janelia-idf/arduino_valve_controller/pcb/arduino_valve_controller.sch

## KiCad design pcb/arduino_valve_controller.sch (2019-02-07)

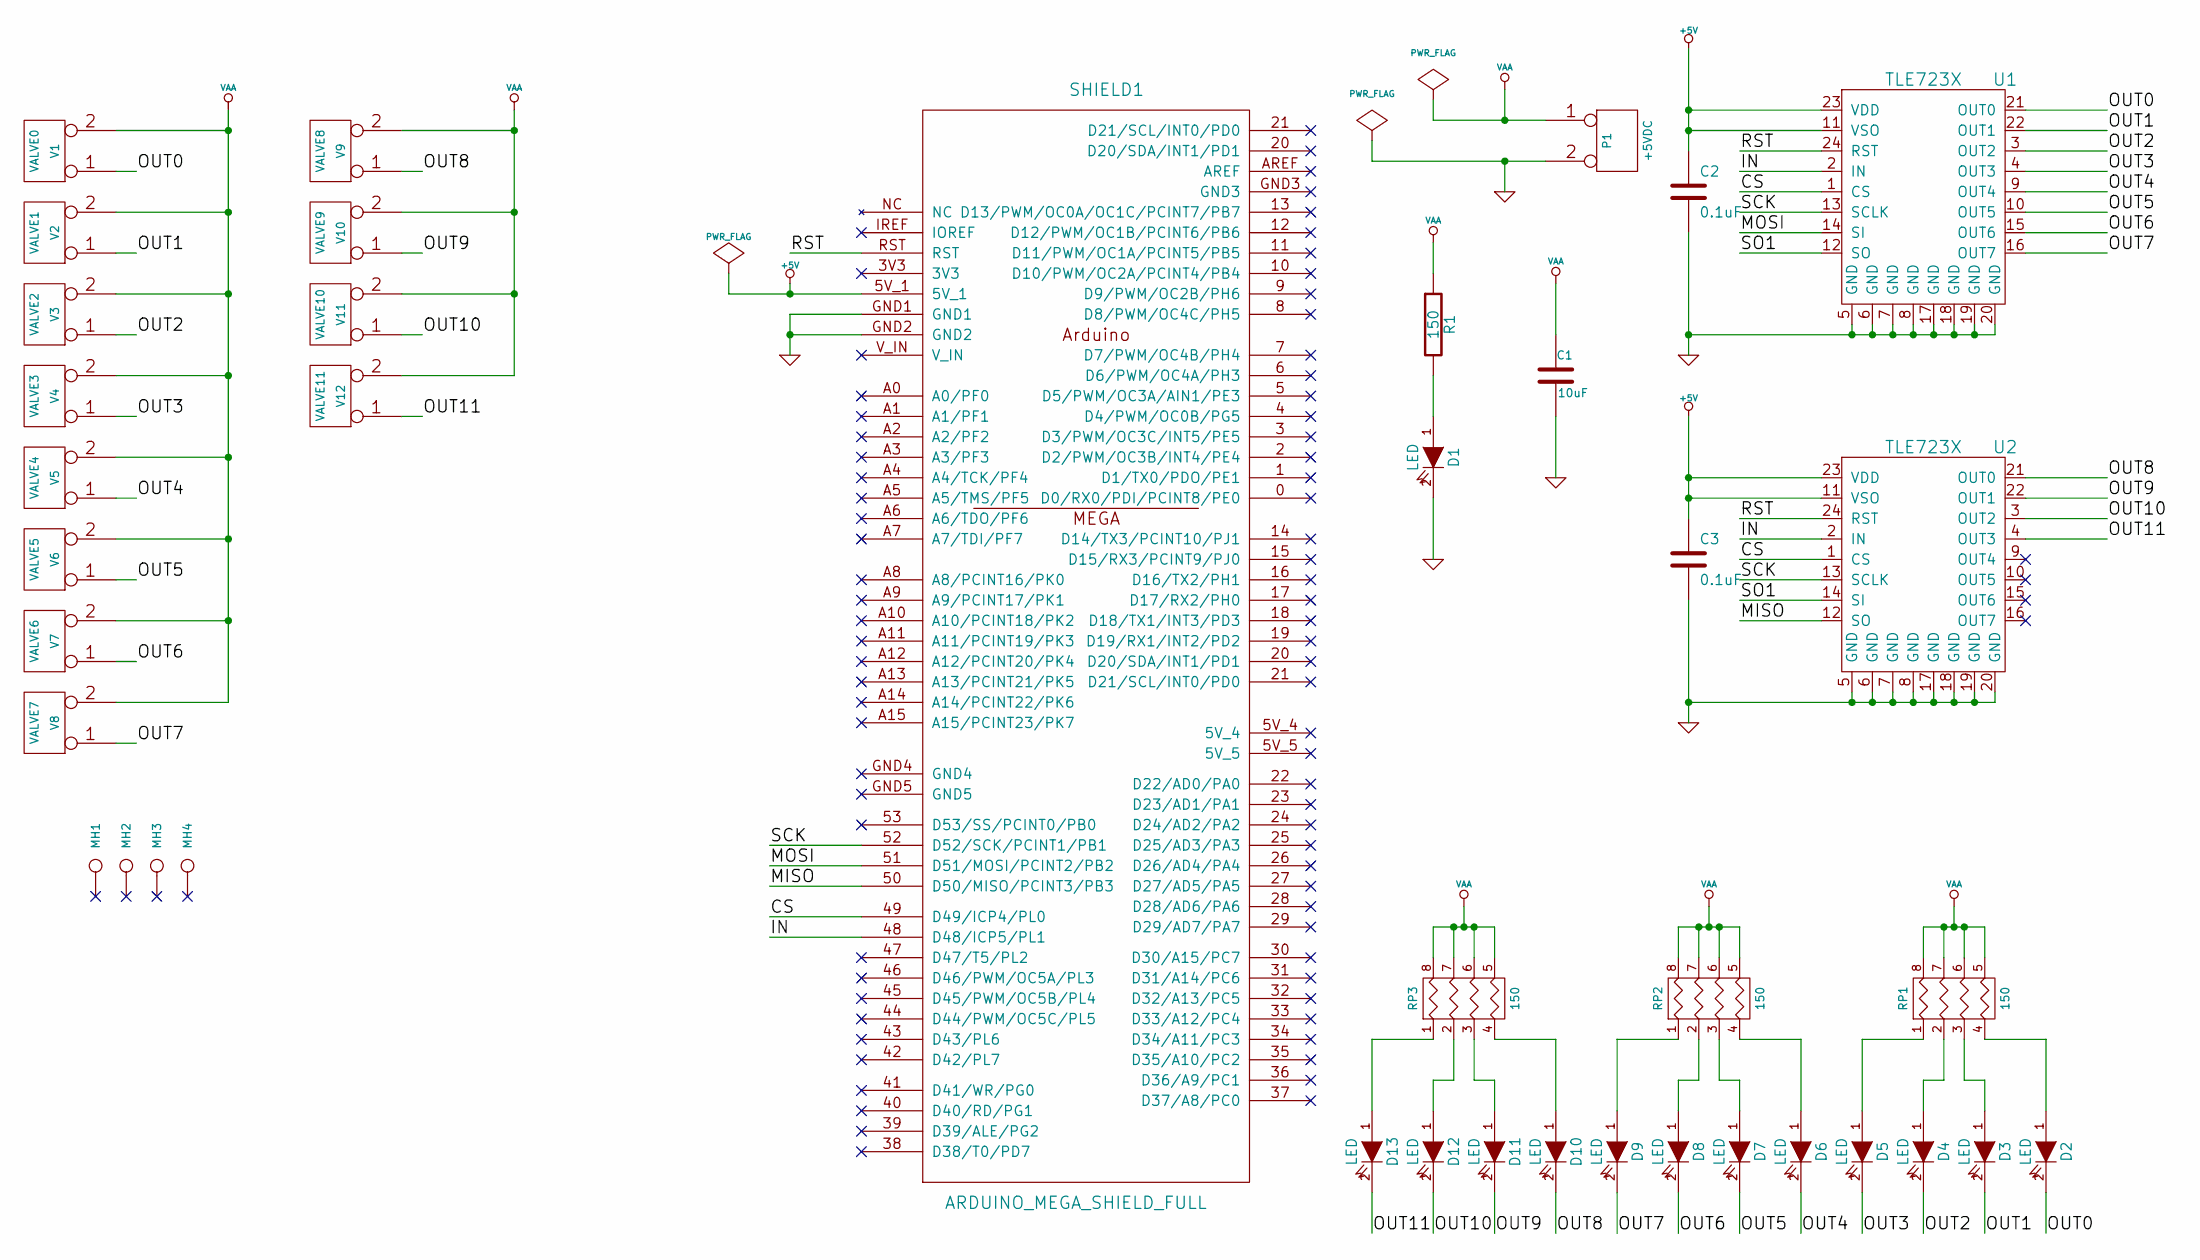
[picture p4: schematic arduino_valve_controller.sch]

Parts:
C1: 10uF
C2, C3: 0.1uF
D1, D2, D3, D4, D5, D6, D7, D8, D9, D10, D11, D12, D13: LED
MH1, MH2, MH3, MH4: CONN_1
P1: +5VDC
R1: 150
RP1, RP2, RP3: 150
SHIELD1: ARDUINO_MEGA_SHIELD_FULL
U1, U2: TLE723X
V1: VALVE0
V2: VALVE1
V3: VALVE2
V4: VALVE3
V5: VALVE4
V6: VALVE5
V7: VALVE6
V8: VALVE7
V9: VALVE8
V10: VALVE9
V11: VALVE10
V12: VALVE11

Connections:
+5V: C2.1, C3.1, SHIELD1.5V_1, U1.11 (VSO), U1.23 (VDD), U2.11 (VSO), U2.23 (VDD)
CS: SHIELD1.49 (D49/ICP4/PL0), U1.1 (CS), U2.1 (CS)
GND: C1.2, C2.2, C3.2, D1.2 (K), P1.2 (PM), SHIELD1.GND1, SHIELD1.GND2, U1.5 (GND), U1.6 (GND), U1.7 (GND), U1.8 (GND), U1.17 (GND), U1.18 (GND), U1.19 (GND), U1.20 (GND), U2.5 (GND), U2.6 (GND), U2.7 (GND), U2.8 (GND), U2.17 (GND), U2.18 (GND), U2.19 (GND), U2.20 (GND)
IN: SHIELD1.48 (D48/ICP5/PL1), U1.2 (IN), U2.2 (IN)
MISO: SHIELD1.50 (D50/MISO/PCINT3/PB3), U2.12 (SO)
MOSI: SHIELD1.51 (D51/MOSI/PCINT2/PB2), U1.14 (SI)
unnamed: D1.1 (A), R1.2
unnamed: D2.1 (A), RP1.4
unnamed: D3.1 (A), RP1.3
unnamed: D4.1 (A), RP1.2
unnamed: D5.1 (A), RP1.1
unnamed: D6.1 (A), RP2.4
unnamed: D7.1 (A), RP2.3
unnamed: D8.1 (A), RP2.2
unnamed: D9.1 (A), RP2.1
unnamed: D10.1 (A), RP3.4
unnamed: D11.1 (A), RP3.3
unnamed: D12.1 (A), RP3.2
unnamed: D13.1 (A), RP3.1
OUT0: D2.2 (K), U1.21 (OUT0), V1.1
OUT1: D3.2 (K), U1.22 (OUT1), V2.1
OUT2: D4.2 (K), U1.3 (OUT2), V3.1
OUT3: D5.2 (K), U1.4 (OUT3), V4.1
OUT4: D6.2 (K), U1.9 (OUT4), V5.1
OUT5: D7.2 (K), U1.10 (OUT5), V6.1
OUT6: D8.2 (K), U1.15 (OUT6), V7.1
OUT7: D9.2 (K), U1.16 (OUT7), V8.1
OUT8: D10.2 (K), U2.21 (OUT0), V9.1
OUT9: D11.2 (K), U2.22 (OUT1), V10.1
OUT10: D12.2 (K), U2.3 (OUT2), V11.1
OUT11: D13.2 (K), U2.4 (OUT3), V12.1
RST: SHIELD1.RST, U1.24 (RST), U2.24 (RST)
SCK: SHIELD1.52 (D52/SCK/PCINT1/PB1), U1.13 (SCLK), U2.13 (SCLK)
SO1: U1.12 (SO), U2.14 (SI)
VAA: C1.1, P1.1, R1.1, RP1.5 (R4), RP1.6 (R3), RP1.7 (R2), RP1.8 (R1), RP2.5 (R4), RP2.6 (R3), RP2.7 (R2), RP2.8 (R1), RP3.5 (R4), RP3.6 (R3), RP3.7 (R2), RP3.8 (R1), V1.2 (PM), V2.2 (PM), V3.2 (PM), V4.2 (PM), V5.2 (PM), V6.2 (PM), V7.2 (PM), V8.2 (PM), V9.2 (PM), V10.2 (PM), V11.2 (PM), V12.2 (PM)
